AgentSarge/salestag/WORKING/softwareV2/main/CMakeLists.minimal.txt

idf_component_register(SRCS "minimal_sd_test.c"
                            INCLUDE_DIRS "."
                            REQUIRES driver fatfs sdmmc esp_timer)
