AgentSarge/salestag/docs/frontend-ui-ux-brainstorming.md

# Frontend UI/UX Workflow Brainstorming Session

**Session Date:** 2025-01-27
**Facilitator:** Business Analyst Mary
**Participant:** User

## Executive Summary

**Topic:** Frontend UI/UX fully completed from start to finish using the BMAD-method

**Session Goals:** Define comprehensive workflow process and identify all components/stages needed for complete frontend UI/UX implementation

**Context:** 
- Solo developer using Claude Code + BMAD-method
- Tech stack: Xcode, VS Code, Supabase Enterprise, Google Workspace
- Timeline: ASAP
- Focus: Broad exploration + component identification

**Techniques Used:** First Principles Thinking

**Status:** Session in progress...

---

## Technique Sessions

### First Principles Thinking - In Progress

**Description:** Breaking down frontend UI/UX completion into fundamental, irreducible components

**Guiding Question:** "What are the most fundamental, irreducible components that MUST exist for completing frontend UI/UX from zero to finished using BMAD-method?"

**Ideas Generated:**
1. **Using the BMAD-method properly** - The foundational requirement that governs all other components
2. **Following the correct user flow for the BMAD-method based on the BMAD-method user guide** - Structured workflow adherence
3. **All proper documented file creations** - Systematic documentation throughout the process
4. **Using all the agents to be able to fully build out the mobile app** - Comprehensive agent utilization for complete development
5. **UI (User Interface)** - Visual elements and interface components
6. **UX (User Experience)** - User flows, interactions, and experience design
7. **Backend database with Supabase** - Data storage and management infrastructure
8. **Edge functions** - Serverless computing capabilities
9. **BLE capabilities** - Bluetooth Low Energy connectivity
10. **Location capabilities** - GPS and location-based services
11. **Notification capabilities** - Push notifications and alerts
12. **Claude Code** - AI-powered development assistant and automation
13. **GitHub repos** - Version control and code repository management
14. **Anything to make it faster** - Speed optimization and efficiency tools

### Insights Discovered:
- Primary focus: **Less human input and higher orchestrated automated agent workflows**
- Emphasis on automation and agent-driven processes to maximize efficiency

---

## Morphological Analysis - Implementation Options

### BMAD-Method Workflow Implementation Approaches:

**Component:** Following correct BMAD-method user flow

**Implementation Options:**
1. **Less human input and higher orchestrated automated agent workflows** - Minimize manual intervention, maximize agent autonomy
2. **Agent-to-agent handoffs for different development phases** - Seamless transitions between specialized agents
3. **Automated code generation based on specifications** - Generate code directly from requirements and designs
4. **Automatic testing and deployment pipelines** - Continuous integration with minimal human oversight
5. **Self-documenting workflows** - Documentation generated automatically throughout the process
6. **Majority human input only in brainstorming phase** - Human involvement concentrated in initial MVP definition and brainstorming, then full automation

### Mobile App Technical Stack Implementation Approaches:

**Component:** UI, UX, Supabase backend, BLE, location, notifications

**Implementation Options:**
1. **All approaches simultaneously** - Cross-platform framework + Native capabilities + Template-based architecture + Component libraries
   - React Native or Flutter for cross-platform base
   - Native modules for BLE and advanced device features
   - Pre-built UI component libraries for rapid development
   - Template-based architecture patterns
   - Automated code generation from design specifications

### Agent Orchestration Implementation Approaches:

**Component:** Automated agent workflows for complete mobile app development

**Recommended Implementation Options:**
1. **Sequential Pipeline with Quality Gates**
   - Business Analyst (MVP definition) → Designer Agent (UI/UX) → Developer Agent (code generation) → Testing Agent (automated testing) → Deployment Agent (CI/CD)
   - Each agent validates previous work before proceeding
   - Built-in rollback capabilities if quality gates fail

2. **Parallel Execution with Coordinator Agent**
   - Master Coordinator Agent manages multiple specialist agents simultaneously
   - UI Agent + Backend Agent + Integration Agent work in parallel
   - Coordinator handles dependencies and synchronization
   - Real-time conflict resolution and integration

3. **Iterative Feedback Loop System**
   - Continuous agent-to-agent feedback and refinement
   - Testing Agent provides feedback to Developer Agent for immediate fixes
   - Designer Agent validates Developer output against UX requirements
   - Automatic iteration until quality thresholds met

---

## SCAMPER Method - Workflow Optimization

**Description:** Systematic improvement of automated agent workflows through structured modification techniques

### S - Substitute: What can we replace to improve automation?

**Substitution Ideas Generated:**
1. **Manual requirements writing** → **AI-generated requirements from brainstorming notes**
2. **Manual code reviews** → **Automated code quality agents**
3. **Manual testing** → **Automated testing agents**
4. **Manual deployment** → **CI/CD pipeline agents**
5. **Individual manual handoffs between agents** → **API-driven automatic handoffs with structured data contracts**

### C - Combine: What can we merge to create better automation?

**My Combine question:** What if we combined multiple automation approaches to create an even more powerful workflow?

For example:
- AI requirements generation + automated code generation = direct brainstorming-to-code pipeline?
- Code quality agents + testing agents = integrated quality assurance system?
- Multiple specialized agents + coordinator = unified development orchestration?

What combinations of your substituted automated processes would create the most streamlined mobile app development workflow?

**Recommended Combinations:**
1. **Brainstorming-to-Deployment Pipeline** - AI requirements generation + automated code generation + CI/CD agents = complete automation from ideas to live app
2. **Integrated Quality System** - Code quality agents + automated testing agents + deployment gates = zero-defect releases
3. **Unified Agent Orchestration** - All specialized agents + master coordinator + API contracts = seamless end-to-end automation

### A - Adapt: What can we adapt from other successful automation models?

**My Adapt question:** What successful automation patterns from other industries or development approaches could we adapt to your BMAD-method mobile app workflow?

For example:
- Manufacturing assembly lines → Development pipeline stages?
- DevOps practices → Agent orchestration patterns?
- AI/ML model training workflows → Iterative app improvement cycles?

What proven automation models could we adapt to make your mobile app development even more efficient?

**Recommended Adaptations:**
1. **Manufacturing Assembly Line** → **Development Pipeline Stages** - Each agent handles one specialized task, passes to next agent with quality checkpoints
2. **DevOps CI/CD Practices** → **Agent Orchestration** - Automated testing, integration, and deployment between every agent handoff
3. **Tesla's Over-the-Air Updates** → **Continuous App Improvement** - Automated updates and feature rollouts post-deployment

### M - Modify: How can we enhance your automation approach?

**Recommended Modifications:**
1. **Enhanced Brainstorming Phase** - Scale up initial brainstorming to capture comprehensive MVP requirements, user stories, and edge cases
2. **Specialized Agent Intelligence** - Each agent enhanced with domain-specific knowledge (UI/UX best practices, mobile optimization, Supabase integration patterns)
3. **Parallel Development Tracks** - Modify timeline to run UI development, backend setup, and testing preparation simultaneously
4. **Real-time Quality Monitoring** - Continuous performance and quality metrics throughout the automated pipeline

### P - Put to Other Uses: How else could this automation approach be applied?

**Recommended Alternative Applications:**
1. **Template Creation** - Use the same automation to generate reusable mobile app templates for future projects
2. **Learning System** - Apply the workflow to teach others rapid mobile app development
3. **Consulting Framework** - Package the approach as a service for other solo developers
4. **Multi-Platform Expansion** - Adapt for web apps, desktop apps, or other digital products

### E - Eliminate: What can we remove to simplify the workflow?

**Recommended Eliminations for V1:**
1. **Complex UI Animations** - Eliminate fancy transitions, focus on functional UI first
2. **Advanced Analytics** - Remove detailed user tracking, keep core functionality only  
3. **Multiple Authentication Methods** - Eliminate social logins, use simple email/password
4. **Offline Data Sync** - Remove complex offline capabilities for MVP
5. **Manual Configuration Steps** - Eliminate any setup requiring human intervention

### R - Reverse: What if we flip the development approach?

**Reverse Concept Approved:** "Build working prototype first, then polish" approach

**User Response:** ✅ **YES - Likes the reverse approach**

**Reverse Implementation:**
- Deploy minimal working app Day 1 with basic functionality
- Agents continuously add features through automated iterations
- Real user feedback drives automatic agent improvements
- Faster time to market with rapid iteration cycles
- "Ship fast, improve automatically" philosophy

**Rearranged Agent Workflow:**
1. **Business Analyst** - Quick MVP definition (30 min brainstorming)
2. **Developer Agent** - Basic working app (Day 1 deployment)
3. **Testing Agent** - Automated testing on live app
4. **Enhancement Agents** - Continuous feature additions
5. **Polish Agent** - UI/UX refinement based on usage data

---

## Idea Categorization & Action Planning

### Immediate Opportunities
*Ready to implement now*

1. **30-Minute MVP Brainstorming Session**
   - Description: Complete comprehensive brainstorming to define core mobile app requirements
   - Why immediate: Foundation for entire automated workflow, uses existing BMAD-method
   - Resources needed: Business Analyst agent, brainstorming techniques, documentation templates

2. **Agent Workflow Setup**
   - Description: Configure parallel execution coordinator agent with specialized sub-agents
   - Why immediate: Infrastructure needed before any development can begin
   - Resources needed: BMAD agent coordination, API contracts between agents

3. **Basic Mobile App Template Selection**
   - Description: Choose React Native or Flutter base with Supabase integration
   - Why immediate: Technical foundation for rapid prototyping approach
   - Resources needed: Framework evaluation, Supabase setup, template customization

### Top 3 Priority Implementation Steps

#### #1 Priority: Complete Comprehensive MVP Brainstorming
- **Rationale:** All automation depends on clear requirements and feature definition
- **Next steps:** Use Business Analyst agent to conduct detailed brainstorming session covering all mobile app aspects
- **Resources needed:** BMAD brainstorming framework, documentation agents, requirements templates
- **Timeline:** Today - 1-2 hours maximum

#### #2 Priority: Setup Automated Agent Workflow Pipeline
- **Rationale:** Core automation infrastructure must be in place before development begins
- **Next steps:** Configure coordinator agent, define agent handoff protocols, test agent communications
- **Resources needed:** BMAD agent orchestration tools, API integration setup, workflow testing
- **Timeline:** 1-2 days after brainstorming completion

#### #3 Priority: Deploy Day 1 Working Prototype
- **Rationale:** "Reverse approach" - get something working immediately to enable iterative improvement
- **Next steps:** Developer agent creates minimal functional app, deploy to testing environment, setup continuous integration
- **Resources needed:** Mobile development framework, Supabase backend, deployment pipeline, basic UI components
- **Timeline:** 2-3 days after agent workflow setup

## Final Workflow Summary

**Complete Frontend UI/UX Development using BMAD-Method:**

**Phase 1: Foundation (Day 1)**
- 30-minute comprehensive brainstorming (Business Analyst agent)
- Agent workflow pipeline setup (Coordinator agent)
- Basic mobile app deployment (Developer agent)

**Phase 2: Automation (Days 2-7)**
- Continuous feature additions (Enhancement agents)
- Automated testing and quality assurance (Testing agents)
- Real-time deployment and updates (CI/CD agents)

**Phase 3: Polish (Ongoing)**
- UI/UX refinement based on usage (Polish agent)
- Performance optimization (Optimization agents)
- Feature expansion based on feedback (Enhancement agents)

**Key Success Factors:**
- Human input concentrated in initial brainstorming only
- All subsequent work fully automated through agent coordination
- "Ship fast, improve automatically" philosophy
- Parallel development tracks for maximum speed
- Continuous deployment with automated quality gates
