AgentSarge/salestag/WORKING/archive/historical-docs/BUILD_SUCCESS_REPORT.md

# SalesTag Phase 1 Build Success Report

## 🎉 BUILD COMPLETED SUCCESSFULLY!

**Date**: August 21, 2025  
**ESP-IDF Version**: v5.2.2  
**Target**: ESP32-S3  
**Firmware**: salestag-diagnostic.bin

## ✅ Build Summary

### **Firmware Size Analysis**
| Component | Size | Usage | Status |
|---|---|---|---|
| **Total Image** | 369,513 bytes (361KB) | - | ✅ Pass |
| **Flash Usage** | 288,399 bytes | 65% free (664KB available) | ✅ Pass |
| **Static IRAM** | 16,383 bytes | 100% used (1 byte remain) | ⚠️ Monitor |
| **D/IRAM** | 67,323 bytes | 19.5% used (278KB free) | ✅ Pass |

### **Memory Breakdown**
- **Code (.text)**: 213,675 bytes
- **Read-only data (.rodata)**: 74,468 bytes  
- **Initialized data (.data)**: 11,952 bytes
- **Uninitialized data (.bss)**: 2,592 bytes

### **Flash Partition Layout**
- **App Partition**: 1MB allocated
- **Used**: 361KB (36%)
- **Free**: 664KB available for future features

## 🔧 What Was Built

### **Complete SalesTag Audio Recording System**
✅ **Phase 1.1**: Real audio capture with dual MAX9814 microphones  
✅ **Phase 1.2**: 10-second recording state machine integration  
✅ **GPIO Interface**: Button (GPIO 4) and LED (GPIO 40) control  
✅ **SD Card Storage**: WAV file generation at 16kHz/16-bit stereo  
✅ **FreeRTOS Integration**: Multi-task audio processing  

### **Components Successfully Integrated**
- **main.c**: Complete recording application (replaces diagnostic)
- **recorder.c**: Audio capture and WAV generation  
- **ui.c**: Button debouncing and LED status
- **sd_storage.c**: FAT32 SD card management
- **wav_writer.c**: WAV file format generation
- **audio_capture.c**: Audio callback framework

## 🚀 Ready for Hardware Testing

### **What You Can Test Now**
1. **Flash the firmware**: `idf.py flash monitor`
2. **Expected boot message**: `=== SalesTag Audio Recording System v1.0 ===`
3. **Button test**: Press → LED ON, 10 seconds → LED OFF
4. **File creation**: Check for `recording_001.wav` on SD card
5. **Audio quality**: Listen to recorded WAV files

### **Hardware Requirements**
- ESP32-S3 development board
- MicroSD card (FAT32 formatted)
- Button connected to GPIO 4 (with pullup)
- LED connected to GPIO 40 (with current limiting resistor)
- MAX9814 microphones on GPIO 9 and GPIO 12 (optional for initial test)

## 📋 Next Steps

### **Phase 1 Validation**
1. Use testing checklist: `docs/phase1-testing-checklist.md`
2. Complete hardware validation: `docs/hardware-validation-guide.md`
3. Validate all 15 test procedures with actual vs expected results

### **Phase 1 Success Criteria**
- [ ] System boots without errors
- [ ] Button triggers recording within 100ms  
- [ ] Recording stops automatically after 10 seconds (±100ms)
- [ ] WAV files created with correct format
- [ ] Audio quality suitable for speech recognition
- [ ] Multiple recording sessions work reliably

### **If Phase 1 Passes → Phase 2**
- File metadata system with JSON companion files
- AES-256 audio encryption  
- Enhanced power management
- Battery voltage monitoring

## 🔍 Technical Details

### **Build Environment**
- **ESP-IDF**: v5.2.2 (confirmed working)
- **Toolchain**: xtensa-esp-elf GCC 13.2.0
- **Python**: 3.13.4
- **Build time**: ~2 minutes on M1 Mac

### **Compilation Status**
```
✅ No compilation errors
✅ No missing dependencies  
✅ All components linked successfully
✅ Flash size within limits
⚠️ IRAM nearly full (1 byte remaining)
```

### **IRAM Usage Warning**
Static IRAM is 100% used with only 1 byte remaining. This is acceptable for Phase 1 but may require optimization for Phase 2 features. Consider:
- Reducing WiFi/BLE stack components if not needed
- Moving some functions to Flash memory
- Optimizing audio buffer sizes

## 🎯 Confidence Level: HIGH

**The firmware is ready for hardware testing.** All components integrated successfully, build completed without errors, and memory usage is within acceptable ranges for Phase 1 functionality.

**Ready Commands:**
```bash
# Navigate to project
cd /Users/self/Desktop/salestag/softwareV2

# Source ESP-IDF environment  
. ~/esp/esp-idf/export.sh

# Flash and monitor
idf.py flash monitor
```

**What to expect**: Complete boot sequence, ready for recording message, and button-triggered 10-second recording cycles.

---
**Status**: ✅ BUILD SUCCESS - READY FOR HARDWARE VALIDATION
