AgentSarge/salestag/docs/stories/2.5.audio-quality-validation.md

# Story 2.5: Audio Quality Validation & Integration Testing

## Status
Approved

## Story
**As a** sales professional,  
**I want** confidence that the recording system works reliably and produces good quality audio,  
**so that** I can depend on the device during important sales interactions.

## Acceptance Criteria
1. Complete end-to-end workflow testing: Button → Audio → WAV → LED
2. Audio quality meets speech recognition standards (clear speech reproduction)
3. No audio dropouts or corruption during 10-second recordings
4. File size consistency matches expected duration (±5% tolerance)
5. WAV files play correctly in standard audio applications
6. Recording system handles multiple sequential recordings without degradation
7. Error conditions gracefully handled with appropriate user feedback
8. System performance validated under realistic usage conditions

## Tasks / Subtasks
- [ ] Implement comprehensive integration testing suite (AC: 1)
  - [ ] Create automated test sequence for complete workflow
  - [ ] Test button press → recording start → timer → file creation → LED feedback
  - [ ] Validate integration of all Phase 2 stories (2.1-2.4)
  - [ ] Create regression tests to ensure Phase 1 functionality preserved
- [ ] Develop audio quality validation tests (AC: 2, 3)
  - [ ] Record test speech samples at various volumes and distances
  - [ ] Analyze audio for clarity, noise levels, and dropouts
  - [ ] Test dual microphone channel quality and balance
  - [ ] Validate audio meets minimum quality standards for speech
- [ ] Implement file consistency validation (AC: 4, 5)
  - [ ] Verify file sizes match expected duration calculations
  - [ ] Test WAV file format compliance with audio standards
  - [ ] Validate files open correctly in VLC, Windows Media Player, QuickTime
  - [ ] Check WAV header metadata accuracy
- [ ] Test system reliability and performance (AC: 6, 8)
  - [ ] Conduct multiple sequential recording tests (10+ recordings)
  - [ ] Test system behavior under various environmental conditions
  - [ ] Validate memory management and resource cleanup
  - [ ] Test battery impact and power consumption during recording
- [ ] Implement error handling validation (AC: 7)
  - [ ] Test SD card full scenarios
  - [ ] Test audio capture failure scenarios
  - [ ] Test button press during active recording
  - [ ] Validate error recovery and user feedback
- [ ] Create validation documentation and procedures (AC: 8)
  - [ ] Document testing procedures for future validation
  - [ ] Create quality standards checklist for audio recordings
  - [ ] Establish performance benchmarks for Phase 2 completion

## Dev Notes

### Relevant Source Tree Information
Based on architecture analysis:
- **Integration Points**: All Phase 2 components (Stories 2.1-2.4)
- **Test Files**: Integration testing framework, validation scripts
- **Dependencies**: Complete Phase 2 implementation, test audio samples

### Critical Technical Details
This story validates the complete Phase 2 implementation and establishes quality standards:
- **Audio Quality**: Clear speech reproduction suitable for business use
- **File Format**: Standard WAV compliance for broad compatibility
- **System Reliability**: Robust operation under realistic conditions
- **Error Handling**: Graceful degradation and user feedback

### Integration Requirements
- **DEPENDS ON** Stories 2.1-2.4 (all Phase 2 components must be complete)
- **VALIDATES** complete workflow from button press to playable audio file
- **ENSURES** Phase 1 functionality remains intact (regression testing)
- **ESTABLISHES** quality standards for Phase 3 development

### Testing Standards and Quality Criteria

**Audio Quality Standards**:
- **Speech Clarity**: Words clearly distinguishable at normal speaking volume
- **Frequency Response**: Adequate for speech (300Hz - 8kHz minimum)
- **Signal-to-Noise Ratio**: >20dB for acceptable speech quality
- **Channel Balance**: Stereo channels within 3dB of each other

**File Format Standards**:
- **WAV Compliance**: Files open correctly in standard audio players
- **Duration Accuracy**: File duration matches recording time (±100ms)
- **File Size**: 320KB ±5% for 10-second recordings
- **Header Integrity**: Valid WAV headers with correct metadata

**System Performance Standards**:
- **Recording Success Rate**: >98% success for button press → valid file
- **Audio Dropout Rate**: <0.1% (no noticeable gaps in 10-second recording)
- **Sequential Recording**: 10+ consecutive recordings without degradation
- **Error Recovery**: System returns to IDLE state after any error condition

### Specific Testing Requirements

**Manual Testing Procedures**:
1. **Speech Quality Test**: Record and play back clear speech at 1-3 feet distance
2. **Environmental Test**: Test in quiet and moderately noisy environments  
3. **Durability Test**: 20+ recordings to test system stability
4. **Cross-Platform Test**: Verify files play on Windows, Mac, mobile devices

**Automated Testing Requirements**:
- Integration test suite covering complete workflow
- File validation scripts for format and size checking
- Regression tests ensuring Phase 1 functionality intact
- Performance monitoring for memory and resource usage

### Validation Criteria for Phase 2 Completion

Phase 2 is complete when:
- [ ] All acceptance criteria for Stories 2.1-2.4 are met
- [ ] Audio quality meets established standards
- [ ] System reliability demonstrates >98% success rate
- [ ] Files are compatible with standard audio applications
- [ ] No regression in Phase 1 functionality
- [ ] Error conditions handled gracefully
- [ ] Documentation and testing procedures established

## Change Log
| Date | Version | Description | Author |
|---|---|---|---|
| 2025-08-22 | 1.0 | Initial story creation for Phase 2 Sprint | Sarah (PO) |

## Dev Agent Record
*This section will be populated by the development agent during implementation*

### Agent Model Used
*To be filled during development*

### Debug Log References
*To be filled during development*

### Completion Notes List
*To be filled during development*

### File List
*To be filled during development*

## QA Results
*Results from QA Agent review will be populated here after implementation*
