AgentSarge/salestag/WORKING/softwareV2/main/audio_capture.h

#pragma once
#include <stddef.h>
#include <stdint.h>
#include "esp_err.h"

#ifdef __cplusplus
extern "C" {
#endif

typedef void (*audio_capture_callback_t)(const int16_t *interleaved_frames, size_t num_frames, void *user_ctx);

// Raw ADC callback for direct access to microphone values (single mic)
typedef void (*raw_adc_callback_t)(uint16_t mic_adc, void *user_ctx);

esp_err_t audio_capture_init(int sample_rate_hz, int channels);
void audio_capture_set_callback(audio_capture_callback_t cb, void *user_ctx);
void audio_capture_set_raw_adc_callback(raw_adc_callback_t cb, void *user_ctx);
esp_err_t audio_capture_start(void);
esp_err_t audio_capture_stop(void);
void audio_capture_deinit(void);

// Direct ADC reading functions (single mic)
esp_err_t audio_capture_read_raw_adc(uint16_t *mic_adc);

#ifdef __cplusplus
}
#endif
